yurikhan/purple-tentacle/schematic/left.sch

## KiCad design schematic/left.sch (2017-03-05)

Schematic: left.sch

Parts:
DA02, DA03, DA04, DA05, DA39: D
DB00, DB01, DB02, DB03, DB04, DB05, DB39, DB99: D
DC00, DC01, DC02, DC03, DC04, DC05, DC39, DC99: D
DD00, DD01, DD02, DD03, DD04, DD05, DD39, DD99: D
DE00, DE01, DE02, DE03, DE04, DE05, DE39, DE99: D
DK00, DK01, DK02, DK03, DK04, DK05, DK06: D
DZ03, DZ05, DZ39: D
SWA02, SWA03, SWA04, SWA05, SWA39: SW_PUSH
SWB00, SWB01, SWB02, SWB03, SWB04, SWB05, SWB39, SWB99: SW_PUSH
SWC00, SWC01, SWC02, SWC03, SWC04, SWC05, SWC39, SWC99: SW_PUSH
SWD00, SWD01, SWD02, SWD03, SWD04, SWD05, SWD93, SWD99: SW_PUSH
SWE00, SWE01, SWE02, SWE03, SWE04, SWE05, SWE39, SWE99: SW_PUSH
SWK00, SWK01, SWK02, SWK03, SWK04, SWK05, SWK06: SW_PUSH
SWZ03, SWZ05, SWZ39: SW_PUSH
