yurikhan/purple-tentacle/schematic/right.sch

## KiCad design schematic/right.sch (2017-03-05)

Schematic: right.sch

Parts:
DA06, DA07, DA08, DA09, DA41: D
DB06, DB07, DB08, DB09, DB10, DB11, DB12, DB41: D
DC06, DC07, DC08, DC09, DC10, DC11, DC12, DC41: D
DD06, DD07, DD08, DD09, DD10, DD11, DD12, DD41: D
DE06, DE07, DE08, DE09, DE10, DE11, DE12, DE41: D
DK07, DK08, DK09, DK10, DK11, DK12, DK13: D
DZ06, DZ08, DZ41: D
SWA06, SWA07, SWA08, SWA09, SWA41: SW_PUSH
SWB06, SWB07, SWB08, SWB09, SWB10, SWB11, SWB12, SWB41: SW_PUSH
SWC06, SWC07, SWC08, SWC09, SWC10, SWC11, SWC12, SWC41: SW_PUSH
SWD06, SWD07, SWD08, SWD09, SWD10, SWD11, SWD12, SWD41: SW_PUSH
SWE06, SWE07, SWE08, SWE09, SWE10, SWE11, SWE12, SWE41: SW_PUSH
SWK07, SWK08, SWK09, SWK10, SWK11, SWK12, SWK13: SW_PUSH
SWZ06, SWZ08, SWZ41: SW_PUSH
