yurikhan/purple-tentacle/schematic/schematic.sch

## KiCad design schematic/schematic.sch (2017-03-05)

Schematic: schematic.sch

Parts:
DA40: LED
DB40: LED
DZ40: LED
RA40: R
RB40: R
RZ40: R
U1: Arduino_Micro
